Lucksly/Team-Conagher-Racing-WRO2025-FUTURE-ENGINEERS/About THE MACHINE/V. Chew pictures/IMG_E1809.JPG

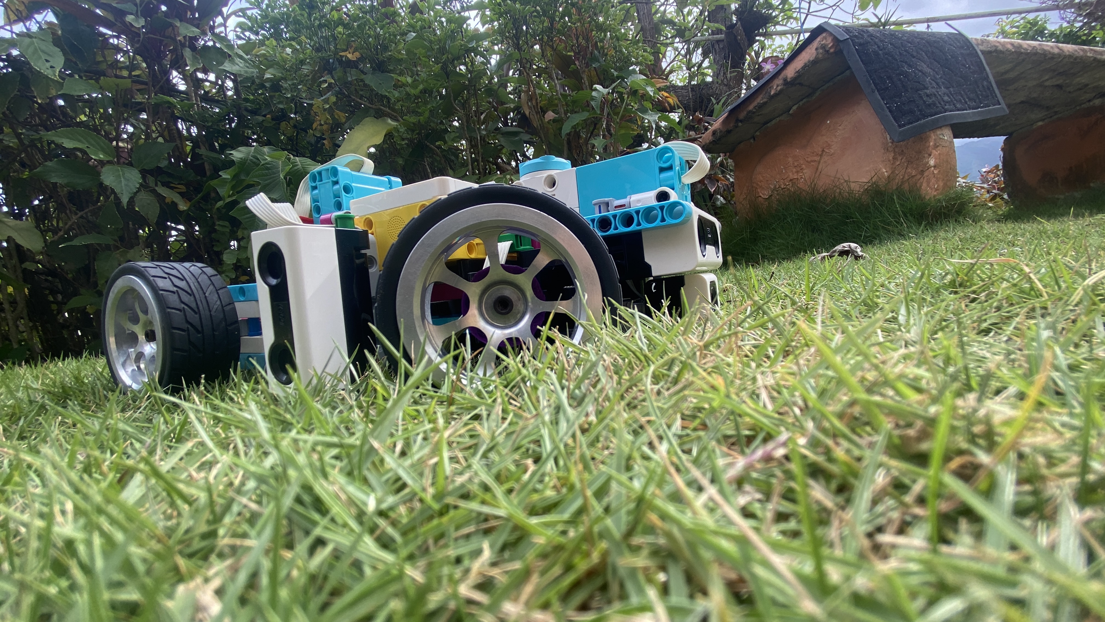
About THE MACHINE/V. Chew pictures/IMG_E1809.JPG
